MOSH-Insa-Toulouse/2022-2023-4gp-nizery-labrousse-cauvet/APK Bluetooth/Code_Bluetooh_Part1.PNG

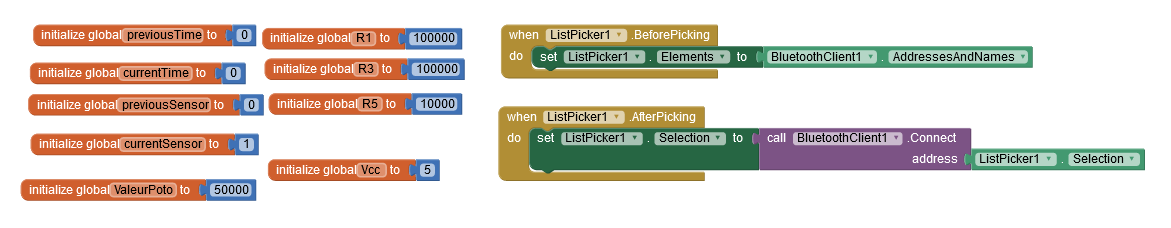
APK Bluetooth/Code_Bluetooh_Part1.PNG
